moritzmhmk/rpi-pico-waterlevel-sensor/src/env.py

WLAN_SSID = "<SOME_SSID>"
WLAN_PASSWORD = "<TOP_SECRET>"

MQTT_SERVER = "homeassistant.local"
MQTT_CLIENT_ID = "rpi-pico-waterlevel-01"
MQTT_STATE_TOPIC = "sensor/waterlevel_01/state"
MQTT_USER = "<USER>"
MQTT_PASSWORD = "<PASSWORD>"
